Raphfriend/USB2DB15/RFUSB_to_DB15/XBoxOneController.cpp

//
// Created by Kitsune on 8/21/2020.
// Modified by Frank_fjs on 10/9/2020.
//

#include "XBoxOneController.h"
#include "device_descriptor.h"

/**
 * Create a new XBoxOneController
 *
 * @param p Pointer to the XBoxOne Controller to Wrap
 */
XBoxOneController::XBoxOneController(XBOXONE *p) {
  xbox = p;
}

/**
 * Gets if the button has been clicked since the last check
 *
 * This function uses the aliases provide by the Host Shield Library
 * to determine if a given button has been clicked. Only returns true
 * once per button press
 *
 * @param button The button to check. Defined in "device_description.h"
 * @return If the button has been clicked
 */
bool XBoxOneController::GetButtonClick(uint8_t button) {
  // Added to fix an issue regarding the USB Host Shield Xbox library
  // XBOXUSB.cpp | Line 291 | bool XBOXUSB::getButtonClick(ButtonEnum b)
  // Creates an issue surrounding L2 & R2 where a false GetButtonClick is registered 
  // upon holding SELECT to enter BIND mode
  // TODO Find the source of the issue and fix properly
  // Frank_fjs 9/10/2020  
  if(!GetButtonState(button)) {
    return false;
  }
  switch(button) {
    case BUTTON_UP:
      return xbox->getButtonClick(UP) || xbox->getAnalogHat(LeftHatY) <= 32767 && xbox->getAnalogHat(LeftHatY) >= 16384;
    case BUTTON_DOWN:
      return xbox->getButtonClick(DOWN) || xbox->getAnalogHat(LeftHatY) >= -32768 && xbox->getAnalogHat(LeftHatY) <= -16384;
    case BUTTON_LEFT:
      return xbox->getButtonClick(LEFT) || xbox->getAnalogHat(LeftHatX) >= -32768 && xbox->getAnalogHat(LeftHatX) <= -16384;
    case BUTTON_RIGHT:
      return xbox->getButtonClick(RIGHT) || xbox->getAnalogHat(LeftHatX) <= 32767 && xbox->getAnalogHat(LeftHatX) >= 16384;
    case BUTTON_START:
      return xbox->getButtonClick(START);
    case BUTTON_COIN:
      return xbox->getButtonClick(BACK);
    case BUTTON_1:
      return xbox->getButtonClick(A);
    case BUTTON_2:
      return xbox->getButtonClick(B);
    case BUTTON_3:
      return xbox->getButtonClick(R2);
    case BUTTON_4:
      return xbox->getButtonClick(X);
    case BUTTON_5:
      return xbox->getButtonClick(Y);
    case BUTTON_6:
      return xbox->getButtonClick(R1);
    case BUTTON_7:
      return xbox->getButtonClick(L1);
    case BUTTON_8:
      return xbox->getButtonClick(L2);
    case BUTTON_9:
      return xbox->getButtonClick(R3);
    case BUTTON_10:
      return xbox->getButtonClick(L3);
  }
  return false;
}

/**
 * Gets the State(pressed or not) of a given button
 *
 * This function uses the aliases provide by the Host Shield Library
 * to determine if a given button is pressed on the controller
 *
 * @param button The button to check. Defined in "device_description.h"
 * @return If the requested button is pressed
 */
bool XBoxOneController::GetButtonState(uint8_t button) {
  switch(button) {
    case BUTTON_UP:
      return xbox->getButtonPress(UP) || xbox->getAnalogHat(LeftHatY) <= 32767 && xbox->getAnalogHat(LeftHatY) >= 16384;
    case BUTTON_DOWN:
      return xbox->getButtonPress(DOWN) || xbox->getAnalogHat(LeftHatY) >= -32768 && xbox->getAnalogHat(LeftHatY) <= -16384;
    case BUTTON_LEFT:
      return xbox->getButtonPress(LEFT) || xbox->getAnalogHat(LeftHatX) >= -32768 && xbox->getAnalogHat(LeftHatX) <= -16384;
    case BUTTON_RIGHT:
      return xbox->getButtonPress(RIGHT) || xbox->getAnalogHat(LeftHatX) <= 32767 && xbox->getAnalogHat(LeftHatX) >= 16384;
    case BUTTON_START:
      return xbox->getButtonPress(START);
    case BUTTON_COIN:
      return xbox->getButtonPress(BACK);
    case BUTTON_1:
      return xbox->getButtonPress(A);
    case BUTTON_2:
      return xbox->getButtonPress(B);
    case BUTTON_3:
      return xbox->getButtonPress(R2);
    case BUTTON_4:
      return xbox->getButtonPress(X);
    case BUTTON_5:
      return xbox->getButtonPress(Y);
    case BUTTON_6:
      return xbox->getButtonPress(R1);
    case BUTTON_7:
      return xbox->getButtonPress(L1);
    case BUTTON_8:
      return xbox->getButtonPress(L2);
    case BUTTON_9:
      return xbox->getButtonPress(R3);
    case BUTTON_10:
      return xbox->getButtonPress(L3);
  }
  return false;
}

/**
 * Checks if an Official XBoxOne controller is connected to the system
 *
 * Checks if a XBoxOne controller is connected to the system. The Vid and Pid
 * of XboxOne Controllers is defined in the Host Shield Library.  Any
 * Controllers not defined as XBoxOne controllers in the library will be
 * treated as generic HID controllers
 *
 * @return true if an XBoxOne controller is connected to the system
 */
bool XBoxOneController::Connected() {
  if (xbox->XboxOneConnected) {
    xbox->setRumbleOff();
    return true;
  }
  return false;
}

/**
 * Gets the Vendor ID for the controller
 *
 * As there is no way to currently get the exact vid out of the XBoxOne
 * Controller Class we will use a hardcoded value. This is one of the possible
 * VIDs for an XBoxOne controller
 *
 * @return The Controller's Vendor ID
 */
uint16_t XBoxOneController::GetVid() {
  return XBOX_VID1;
}

/**
 * Gets the Product ID for the controller
 *
 * As there is no way to currently get the exact vid out of the XBoxOne
 * Controller Class we will use a hardcoded value. This is one of the possible
 * VIDs for an XBoxOne controller
 *
 * @return The Controller's Product ID
 */
uint16_t XBoxOneController::GetPid() {
  return XBOX_ONE_PID1;
}
