Raphfriend/USB2DB15/RFUSB_to_DB15/debug.h

//
// Created by Frank_fjs on 7/10/2020.
//

/**
 * Reduce or completely disable serial output
 * Uncomment #define REDUCED_SERIAL_OUTPUT & Uncomment #define RELEASE_MODE for DISABLED SERIAL OUTPUT
 * Uncomment #define REDUCED_SERIAL_OUTPUT & Comment   #define RELEASE_MODE for REDUCED SERIAL OUTPUT
 * Comment   #define REDUCED_SERIAL_OUTPUT & Comment   #define RELEASE_MODE for FULL SERIAL OUTPUT
 */
 
#define REDUCED_SERIAL_OUTPUT
//#define RELEASE_MODE
